fabiobaltieri/5p-switch/firmware-usb/requests.h

#define CUSTOM_RQ_READ_REG		0x00
#define CUSTOM_RQ_WRITE_REG		0x01
#define CUSTOM_RQ_GET_PORT_STATUS	0x02
/* #define CUSTOM_RQ_SET_PORT_STATUS	0x03 */
#define CUSTOM_RQ_GET_DM		0x04
#define CUSTOM_RQ_GET_VLAN		0x05
/* #define CUSTOM_RQ_SET_VLAN		0x06 */
#define CUSTOM_RQ_GET_MIB		0x07

#define CUSTOM_RQ_RESET			0xff
